jnbli/EE-Emerge-2020-SnapLights/documentation/Enclosure & Parts Reference Pictures/Frame/Front.jpg

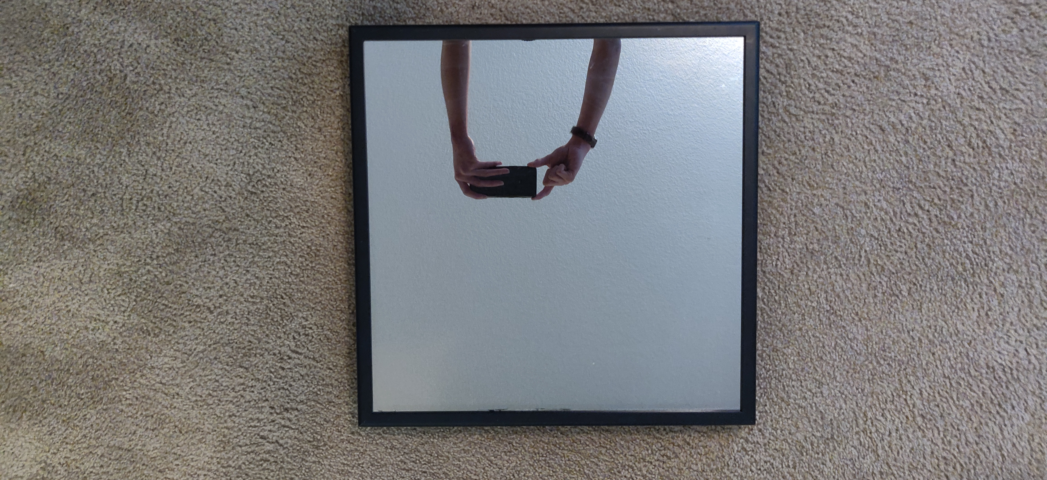
documentation/Enclosure & Parts Reference Pictures/Frame/Front.jpg
