jnbli/EE-Emerge-2020-SnapLights/documentation/Enclosure & Parts Reference Pictures/Microphone/Mic_Front.jpg

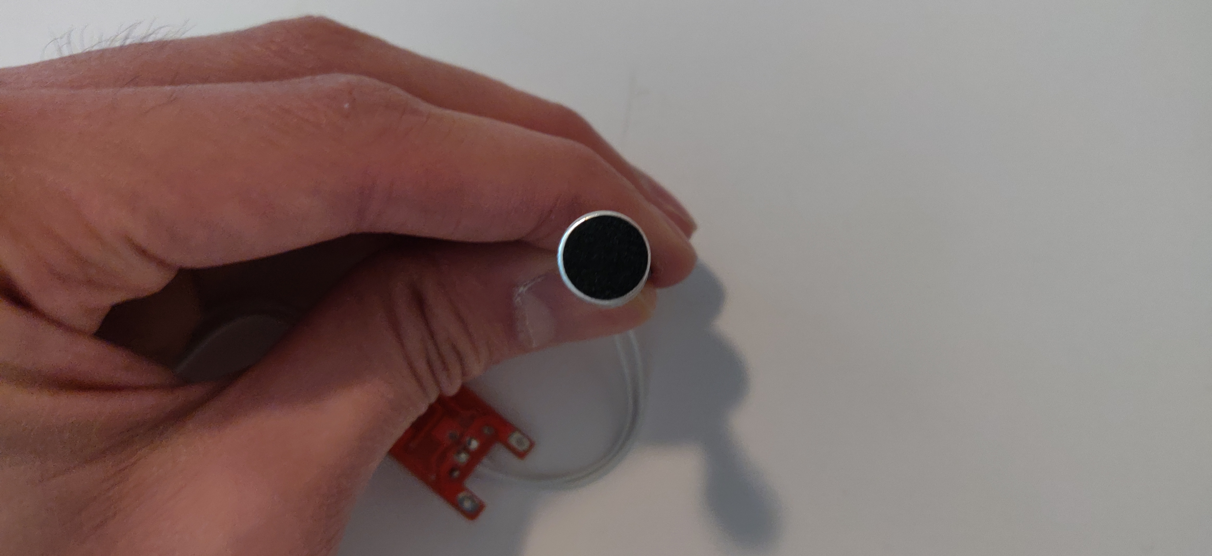
documentation/Enclosure & Parts Reference Pictures/Microphone/Mic_Front.jpg
