jnbli/EE-Emerge-2020-SnapLights/documentation/Enclosure & Parts Reference Pictures/Microphone/Mic_Side.jpg

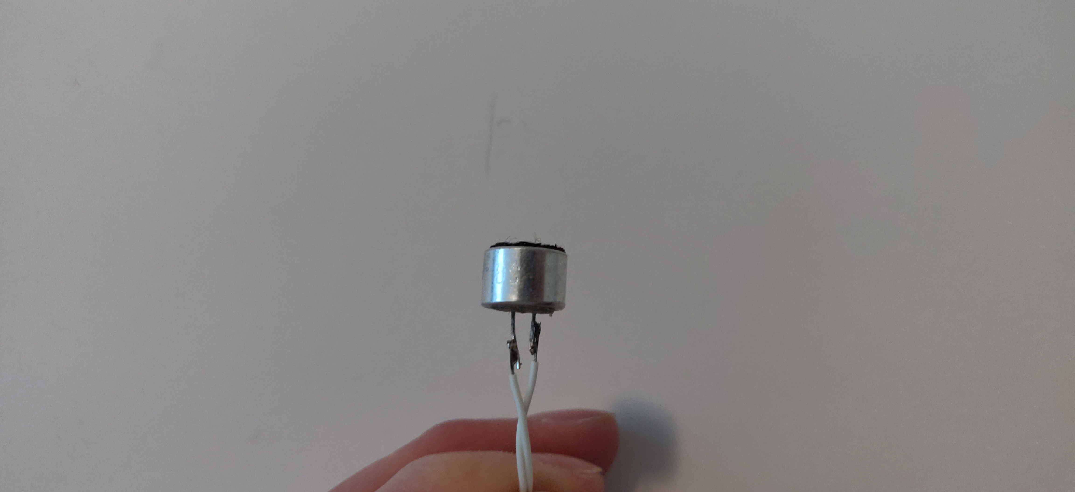
documentation/Enclosure & Parts Reference Pictures/Microphone/Mic_Side.jpg
