jnbli/EE-Emerge-2020-SnapLights/documentation/Enclosure & Parts Reference Pictures/Neopixel/Front.jpg

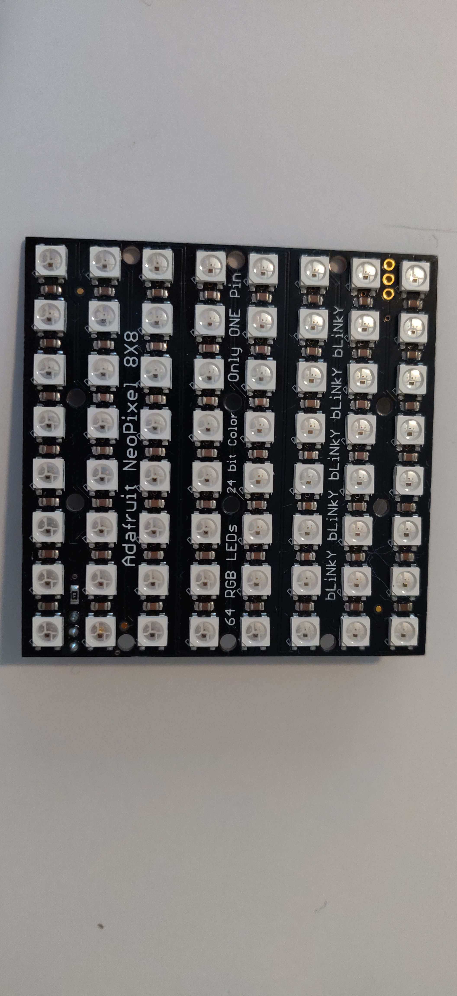
documentation/Enclosure & Parts Reference Pictures/Neopixel/Front.jpg
