jnbli/EE-Emerge-2020-SnapLights/documentation/wiring_diagram.jpg

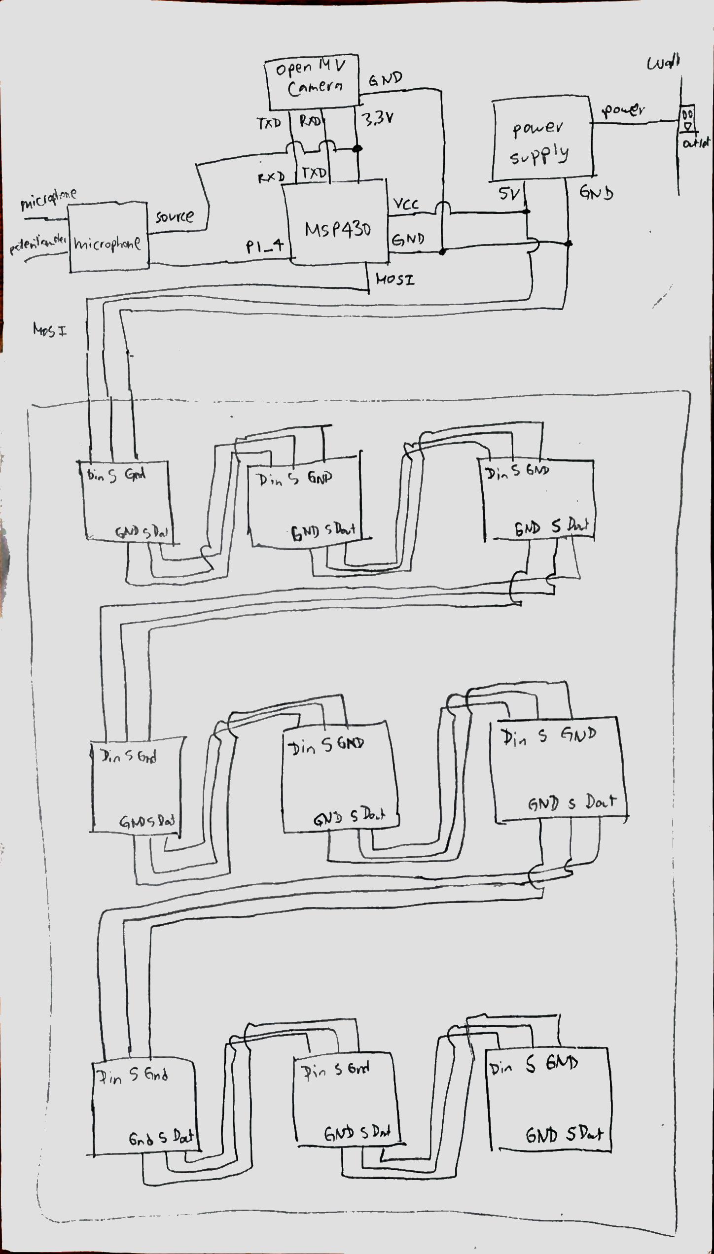
documentation/wiring_diagram.jpg
